DeuceEFI/Amplifier/Amplifier.sch

## KiCad design Amplifier.sch (2013-06-03)

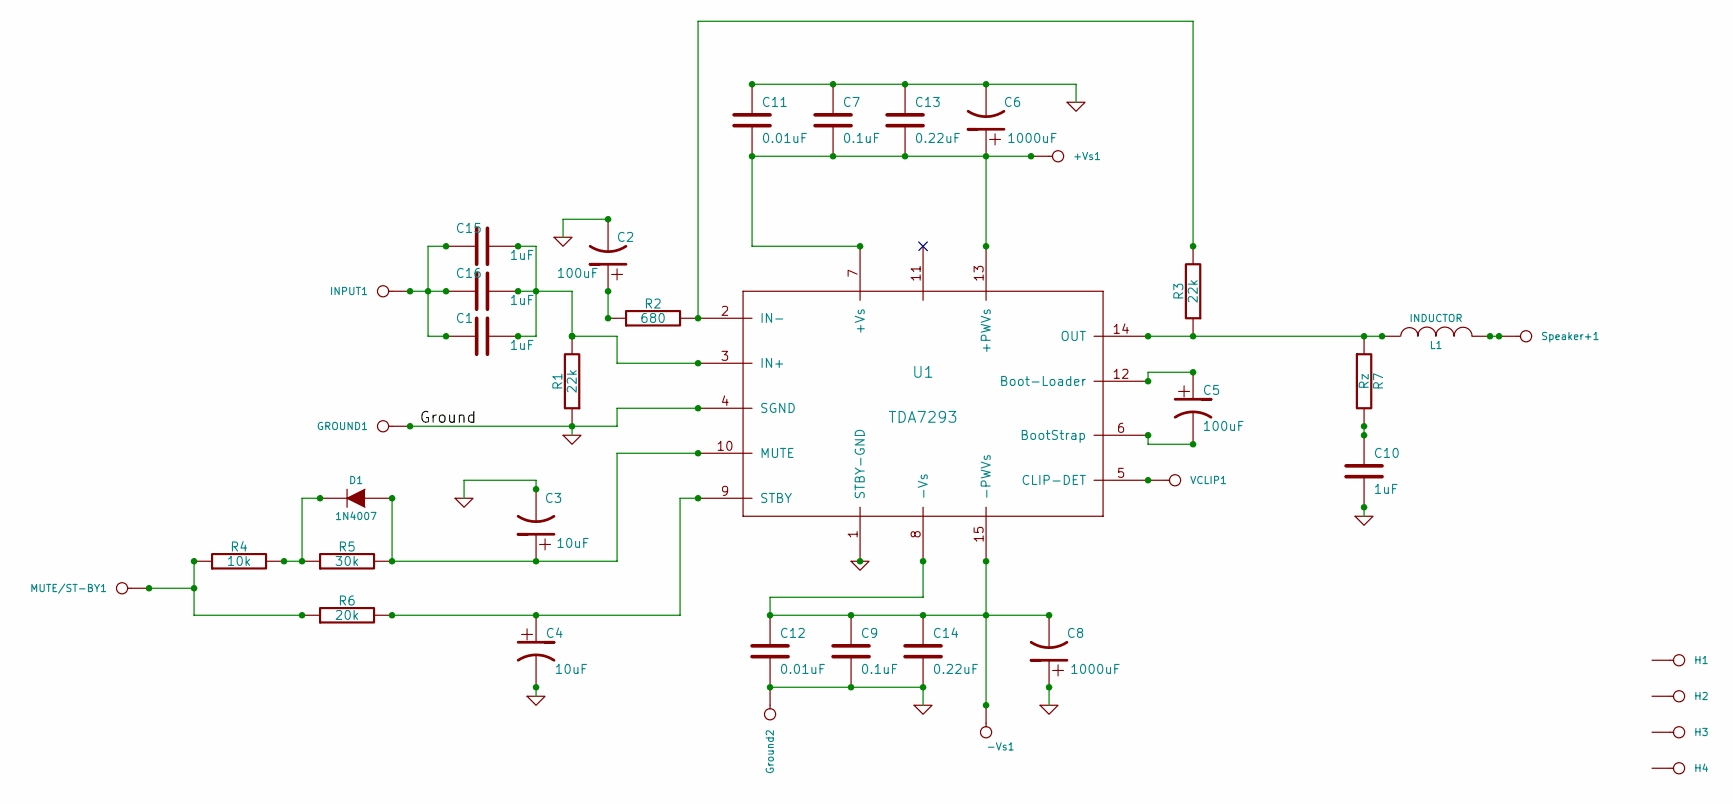
[picture p2: schematic Amplifier.sch]

Parts:
+Vs1: CONN_1
-Vs1: CONN_1
C1, C10, C15, C16: 1uF
C2, C5: 100uF
C3, C4: 10uF
C6, C8: 1000uF
C7, C9: 0.1uF
C11, C12: 0.01uF
C13, C14: 0.22uF
D1: 1N4007
GROUND1: CONN_1
Ground2: CONN_1
H1, H2, H3, H4: CONN_1
INPUT1: CONN_1
L1: INDUCTOR
MUTE/ST-BY1: CONN_1
R1, R3: 22k
R2: 680
R4: 10k
R5: 30k
R6: 20k
R7: Rz
Speaker+1: CONN_1
U1: TDA7293
VCLIP1: CONN_1

Connections:
GND: C2.2 (-), C3.2 (-), C4.2 (-), C6.2 (-), C7.1, C8.1 (+), C9.2, C10.2, C11.1, C12.2, C13.1, C14.2, GROUND1.1, Ground2.1, R1.1, U1.1 (STBY-GND), U1.4 (SGND)
unnamed: +Vs1.1, C6.1 (+), C7.2, C11.2, C13.2, U1.7 (+Vs), U1.13 (+PWVs)
unnamed: -Vs1.1, C8.2 (-), C9.1, C12.1, C14.1, U1.8 (-Vs), U1.15 (-PWVs)
unnamed: C1.1, C15.1, C16.1, R1.2, U1.3 (IN+)
unnamed: C1.2, C15.2, C16.2, INPUT1.1
unnamed: C2.1 (+), R2.1
unnamed: C3.1 (+), D1.1 (A), R5.2, U1.10 (MUTE)
unnamed: C4.1 (+), R6.2, U1.9 (STBY)
unnamed: C5.1 (+), U1.12 (Boot-Loader)
unnamed: C5.2 (-), U1.6 (BootStrap)
unnamed: C10.1, R7.2
unnamed: D1.2 (K), R4.2, R5.1
unnamed: L1.1, R3.1, R7.1, U1.14 (OUT)
unnamed: L1.2, Speaker+1.1
unnamed: MUTE/ST-BY1.1, R4.1, R6.1
unnamed: R2.2, R3.2, U1.2 (IN-)
unnamed: U1.5 (CLIP-DET), VCLIP1.1
